PaulStoffregen/O_C_T41/datasheets/oled13.jpeg

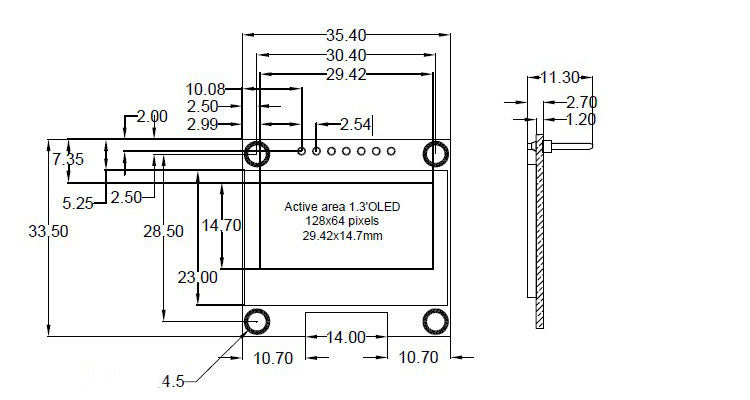
datasheets/oled13.jpeg
