PaulStoffregen/O_C_T41/datasheets/oled13b.png

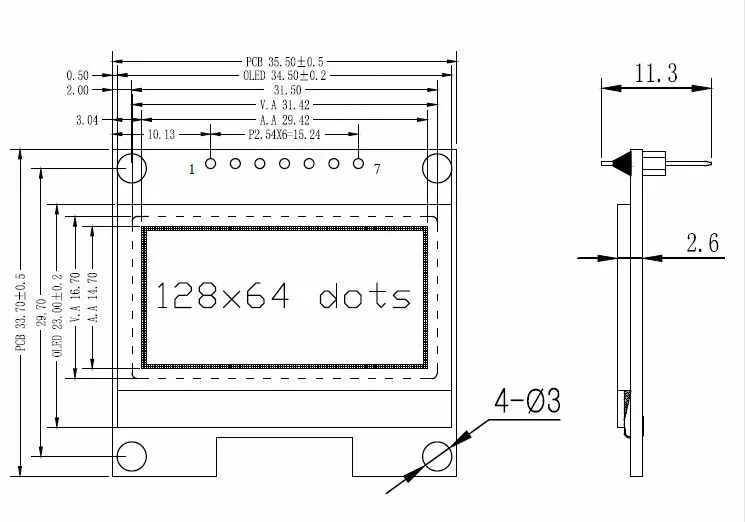
datasheets/oled13b.png
