PaulStoffregen/O_C_T41/pcb/analog_back.jpg

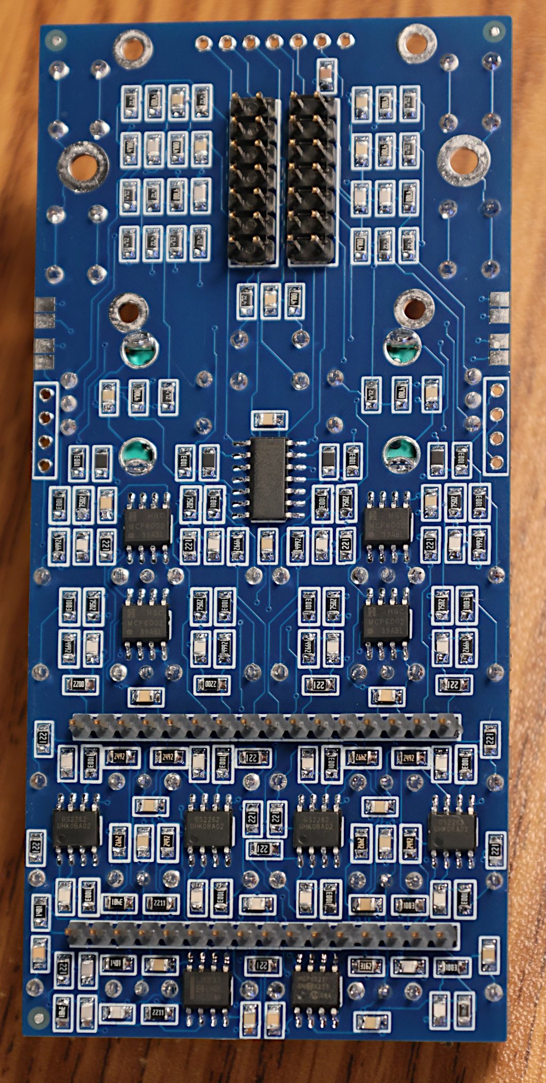
pcb/analog_back.jpg
