PaulStoffregen/O_C_T41/pcb/control_back.jpg

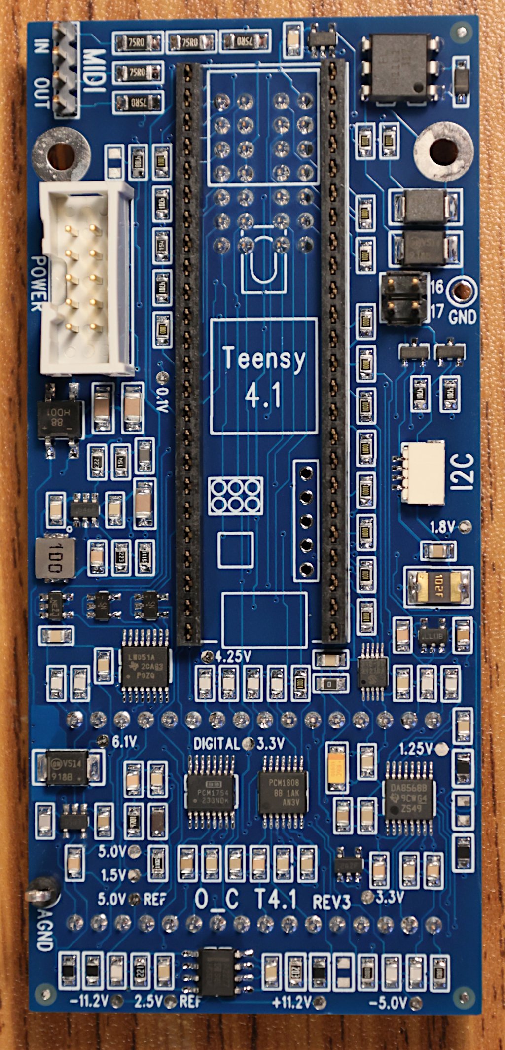
pcb/control_back.jpg
