PaulStoffregen/O_C_T41/pcb/extra/OCT41_auxpanel_midi_usb.jpg

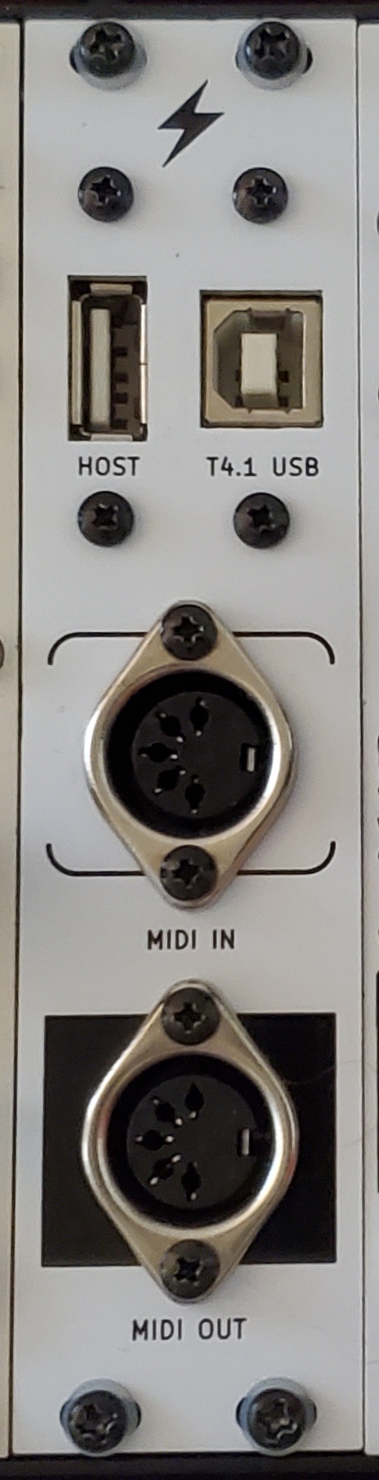
pcb/extra/OCT41_auxpanel_midi_usb.jpg
