PaulStoffregen/O_C_T41/pictures/14hp_panel.jpg

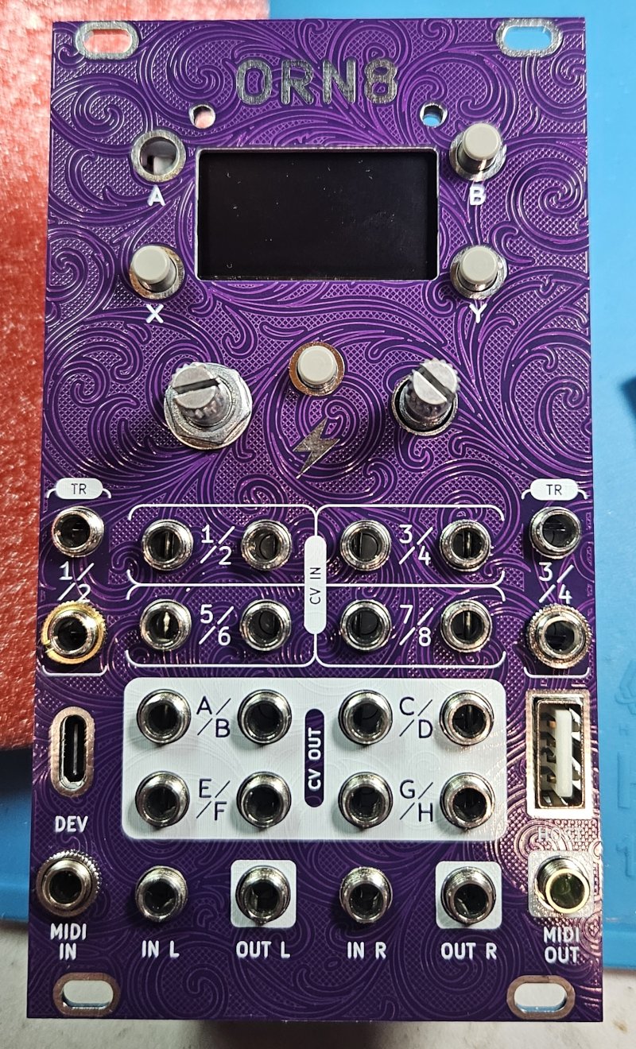
pictures/14hp_panel.jpg
