PaulStoffregen/O_C_T41/pictures/front_panel_desc.png

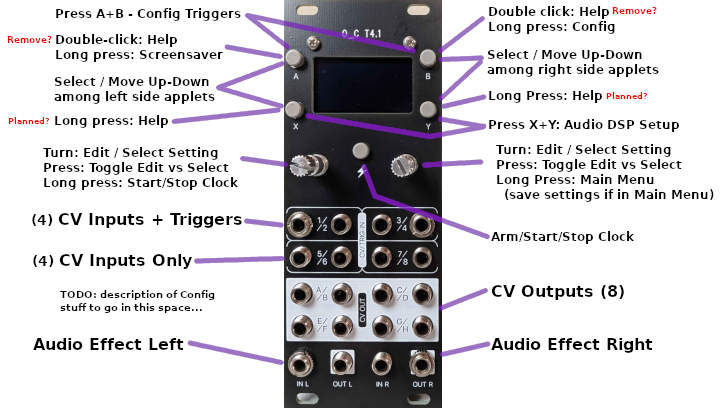
pictures/front_panel_desc.png
