PaulStoffregen/O_C_T41/hardware_tests/O_C_WavFilePlayer/O_C_WavFilePlayer.ino

#include <Audio.h>
#include <SD.h>

AudioPlaySdWav           playWav1;
AudioOutputI2S2          audioOutput;
AudioConnection          patchCord1(playWav1, 0, audioOutput, 0);
AudioConnection          patchCord2(playWav1, 1, audioOutput, 1);

void setup() {
  Serial.begin(9600);

  // Audio connections require memory to work.  For more
  // detailed information, see the MemoryAndCpuUsage example
  AudioMemory(8);

  if (!(SD.begin(BUILTIN_SDCARD))) {
    // stop here, but print a message repetitively
    while (1) {
      Serial.println("Unable to access the SD card");
      delay(500);
    }
  }
}

void playFile(const char *filename)
{
  Serial.print("Playing file: ");
  Serial.println(filename);

  // Start playing the file.  This sketch continues to
  // run while the file plays.
  playWav1.play(filename);

  // A brief delay for the library read WAV info
  delay(25);

  // Simply wait for the file to finish playing.
  while (playWav1.isPlaying()) {
  }
}


void loop() {
  playFile("SDTEST1.WAV");  // filenames are always uppercase 8.3 format
  delay(500);
  playFile("SDTEST2.WAV");
  delay(500);
  playFile("SDTEST3.WAV");
  delay(500);
  playFile("SDTEST4.WAV");
  delay(1500);
}
